indeedhat/media_knob/src/main.h

#define MEDIA_DEBOUNCE_TIME 300
#define MEDIA_DOUBLE_TAP_INTERVAL 500

#define SCROLL_POLL_DELAY 10
#define MEDIA_POLL_DELAY 160

#define SETTINGS_MODE "mode"
//#define SAVE_MODE_STATE


enum op_modes {
	MODE_SCROLL,
	MODE_MEDIA,
#if defined CONFIG_KNOBLET_ENABLE_MACRO_MODE
	MODE_MACRO,
#endif
	MODE_COUNT,
};


typedef struct {
	const struct device *as5600;
} devices;
